hephaestushex/HexBoard/cad/Left Plate.step

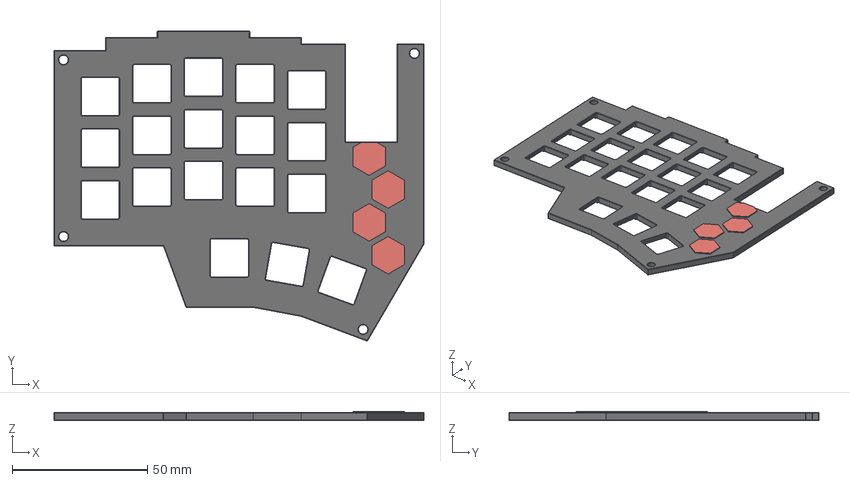
[picture p30: CAD file, 2025-06-24]
cad/Left Plate.step
136.5 x 114.4 x 3.40 mm
